Byvm815/ErgoX84/firmware/ergox_rs/src/macros.rs

macro_rules! config_matrix_pins_rp {
    (peripherals: $p:ident, input: [$($in_pin:ident), *], output: [$($out_pin:ident), +]) => {
        {
            let mut output_pins = [$(Output::new(AnyPin::from($p.$out_pin), embassy_rp::gpio::Level::Low)), +];
            let input_pins = [$(Input::new(AnyPin::from($p.$in_pin), embassy_rp::gpio::Pull::Down)), +];
            output_pins.iter_mut().for_each(|p| {
                p.set_low();
            });
            (input_pins, output_pins)
        }
    };
}
